mbrenn3/3D-printed-oxygen-devices/CAD/cross-section-render.png

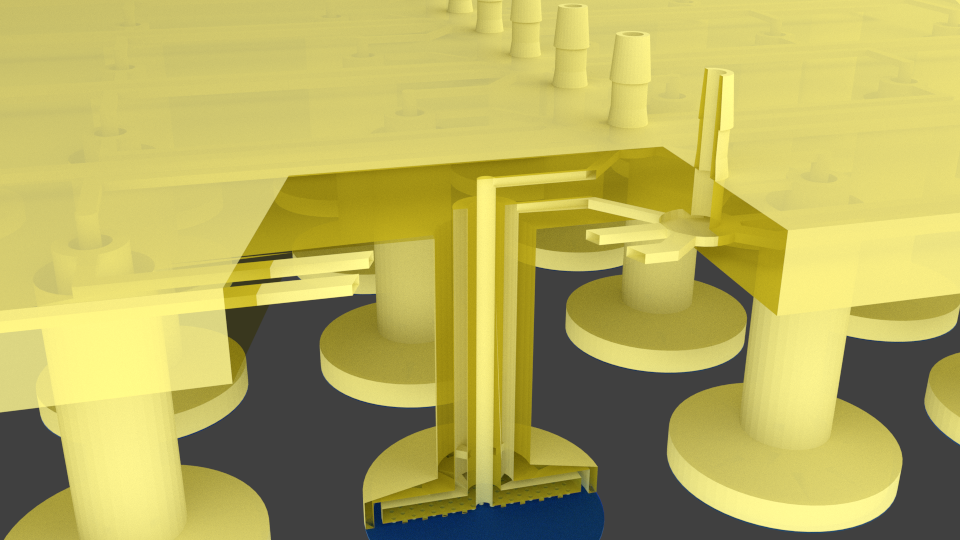
CAD/cross-section-render.png
