mbrenn3/3D-printed-oxygen-devices/publishing/figures/3D-distribution.tiff

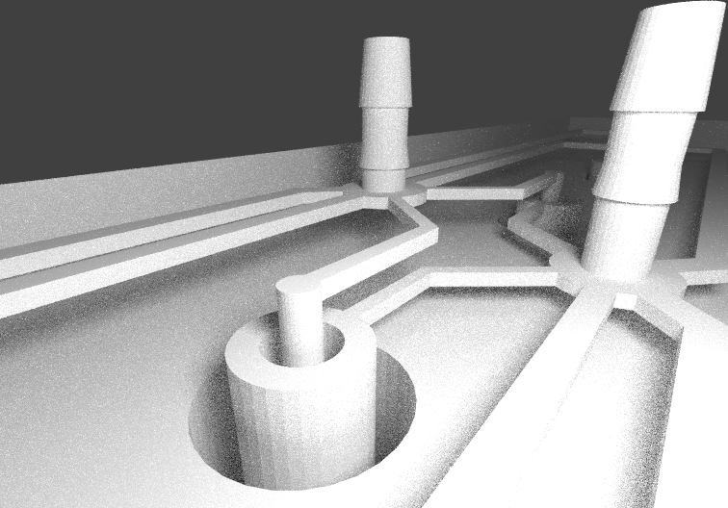
publishing/figures/3D-distribution.tiff
