mbrenn3/3D-printed-oxygen-devices/publishing/figures/24well.JPG

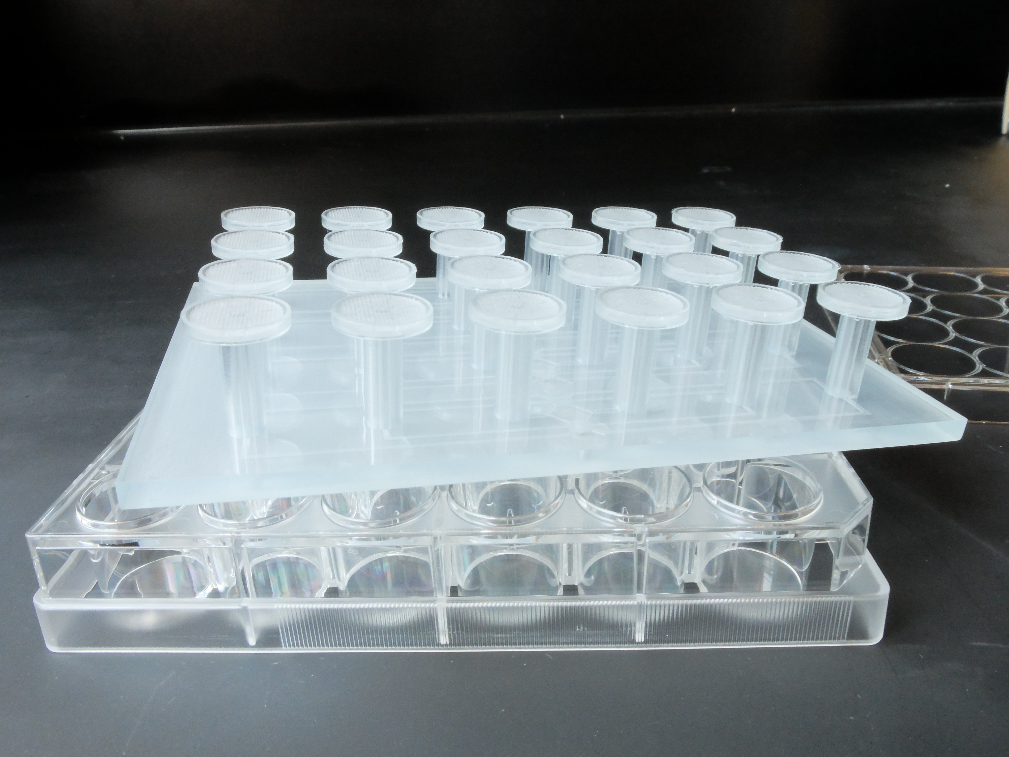
publishing/figures/24well.JPG
