mbrenn3/3D-printed-oxygen-devices/publishing/figures/network-render.png

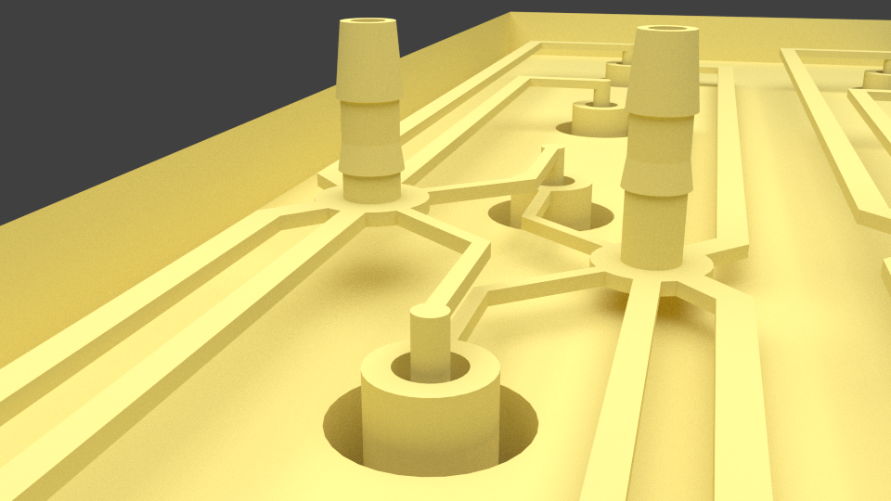
publishing/figures/network-render.png
