mbrenn3/3D-printed-oxygen-devices/publishing/figures/piller-well-render-with-arrows.png

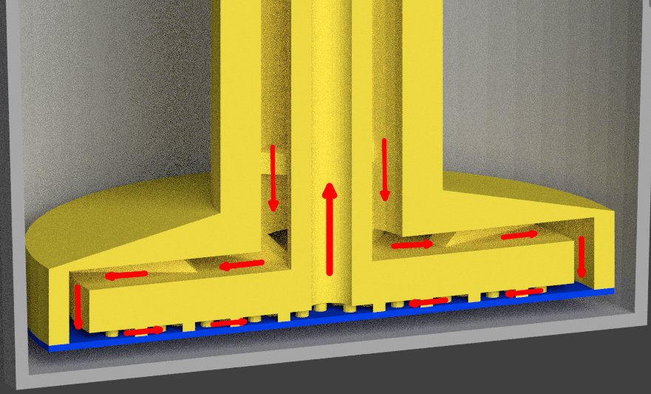
publishing/figures/piller-well-render-with-arrows.png
