mbrenn3/3D-printed-oxygen-devices/uTAS2014/nof3.png

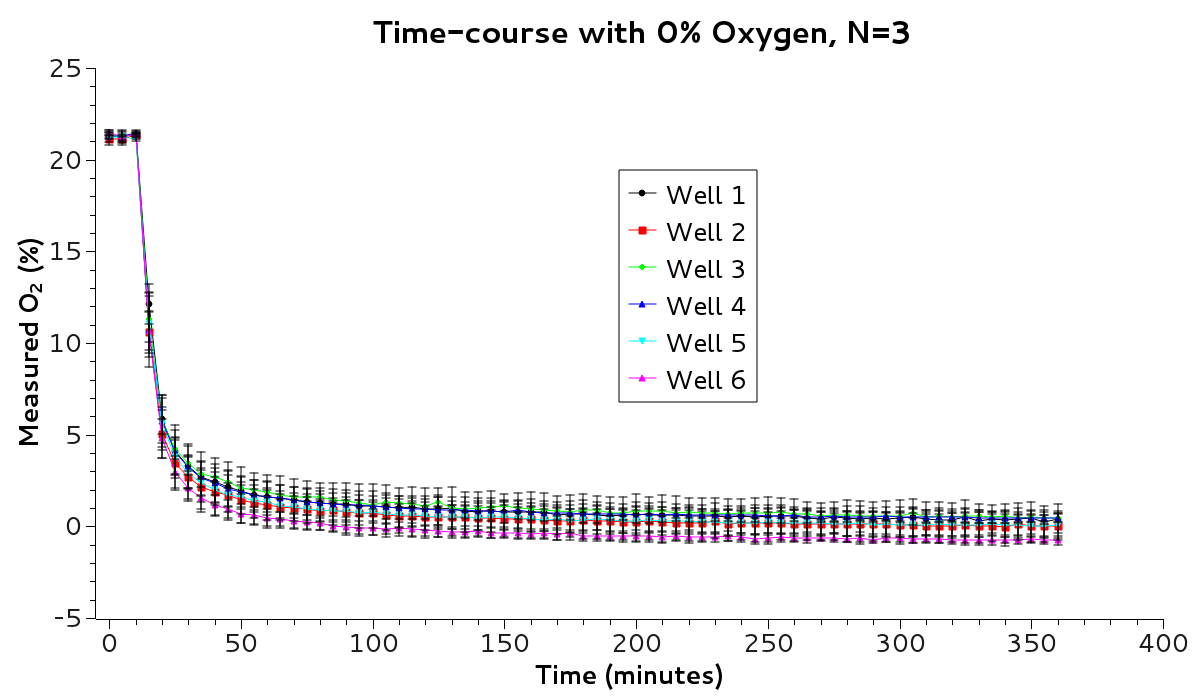
uTAS2014/nof3.png
