mbrenn3/3D-printed-oxygen-devices/presentation-figures/printed-network.JPG

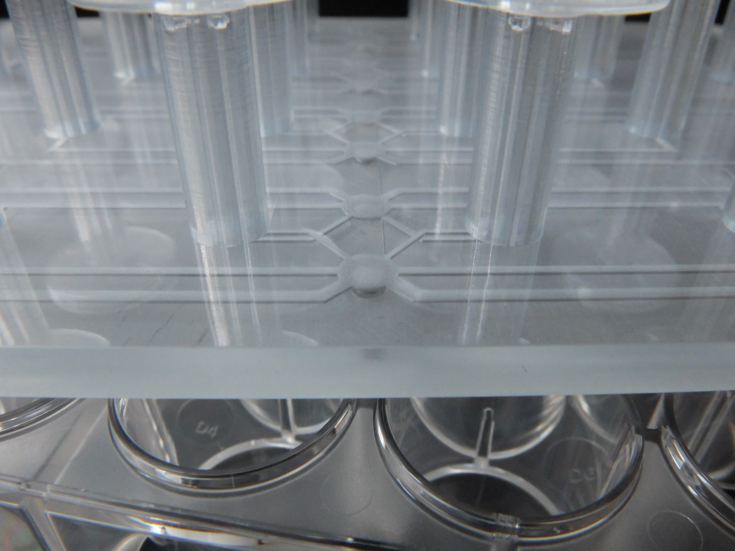
presentation-figures/printed-network.JPG
