mbrenn3/3D-printed-oxygen-devices/publishing/figures/printed-network-crop.jpg

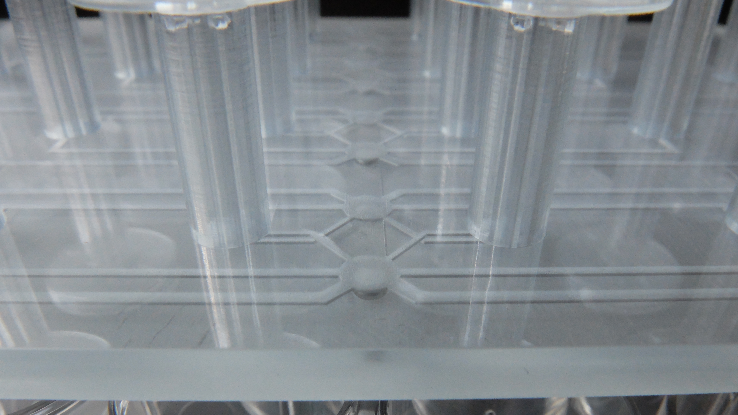
publishing/figures/printed-network-crop.jpg
