mbrenn3/3D-printed-oxygen-devices/data/openwell/Results.xls

 | Area | Mean | Min | Max
1 | 3234 | 452.960 | 405 | 538
2 | 3234 | 452.758 | 406 | 531
3 | 3234 | 453.487 | 413 | 542
4 | 3234 | 454.198 | 414 | 545
5 | 3234 | 454.301 | 402 | 529
6 | 3234 | 454.300 | 416 | 535
7 | 3234 | 454.433 | 408 | 542
8 | 3234 | 454.721 | 412 | 533
9 | 3234 | 455.158 | 412 | 525
10 | 3234 | 456.400 | 413 | 537
11 | 3234 | 457.477 | 413 | 537
12 | 3234 | 457.945 | 407 | 549
13 | 3234 | 458.412 | 414 | 539
14 | 3234 | 459.166 | 420 | 537
15 | 3234 | 459.358 | 413 | 527
16 | 3234 | 459.620 | 417 | 533
17 | 3234 | 459.628 | 415 | 534
18 | 3234 | 460.054 | 413 | 538
19 | 3234 | 460.567 | 415 | 537
20 | 3234 | 460.468 | 418 | 548
21 | 3234 | 460.505 | 420 | 536
22 | 3234 | 460.313 | 422 | 545
23 | 3234 | 460.321 | 414 | 553
24 | 3234 | 460.386 | 421 | 536
25 | 3234 | 460.447 | 418 | 552
26 | 3234 | 461.059 | 404 | 534
27 | 3234 | 461.091 | 419 | 546
28 | 3234 | 461.418 | 420 | 541
29 | 3234 | 461.741 | 415 | 557
30 | 3234 | 461.862 | 413 | 553
31 | 3234 | 461.785 | 420 | 542
32 | 3234 | 462.727 | 420 | 545
33 | 3234 | 462.504 | 422 | 547
34 | 3234 | 462.194 | 401 | 542
35 | 3234 | 462.325 | 419 | 545
36 | 3234 | 462.620 | 415 | 549
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
